calvinkatoroy/pandu-capstone/weekly/WEEK_3/LAPORAN PEKANAN INDIVIDU - Calvin Wirathama Katoroy - Pekan 3.docx

# LAPORAN PEKANAN INDIVIDU

## Capstone Project Desain Proyek 2

### A. Identitas Mahasiswa

Item | Keterangan
Nama | Calvin Wirathama Katoroy
NPM | 2306242395
Program Studi | Teknik Elektro
Kelompok | 13
Judul Proyek | P.A.N.D.U (Perangkat Alarm Nirkabel Deteksi Urgensi)
Pekan ke- | 3
Periode Tanggal | 7 - 12 September 2026
Dosen Pembimbing | Tomy Abuzairi, S.T., M.Sc., Ph.D.

## B. Target Mingguan

Target yang direncanakan pada awal pekan berdasarkan WBS dan pembagian tugas kelompok.

No | Target Pekerjaan | Luaran yang Diharapkan | Status
1 | Melakukan persiapan perancangan mockup dashboard awal sesuai layout device yang akan ditentukan | Wireframe/referensi desain dashboard monitoring | ☐ Belum ☑ Selesai
2 | Mendukung review skematik rangkaian Vest Node, Helmet Node, dan Edge Gateway bersama tim hardware | Masukan teknis kebutuhan data untuk dashboard | ☐ Belum ☑ Selesai
3 | Memantau kelanjutan finalisasi system design tim sebelum tahap procurement | Catatan hasil review desain sistem | ☐ Belum ☑ Selesai

## C. Logbook Aktivitas Harian

Hari/Tanggal | Uraian Aktivitas | Waktu (Jam) | Bukti/Dokumen
Senin (7 Sep) | Mengumpulkan referensi UI/UX dashboard monitoring perangkat wearable & tracking untuk acuan desain P.A.N.D.U | 3 | Kumpulan referensi desain
Selasa (8 Sep) | Menyusun wireframe awal layout dashboard (peta live tracking, status alarm, log insiden) | 4 | Sketsa wireframe dashboard
Rabu (9 Sep) | Diskusi dengan tim hardware terkait data yang dihasilkan skematik Vest Node & Helmet Node untuk kebutuhan tampilan dashboard | 3 | Notulensi diskusi
Kamis (10 Sep) | Merancang mockup dashboard awal menggunakan Figma sesuai draft layout device | 5 | Draft mockup dashboard (Figma)
Jumat (11 Sep) | Meninjau hasil skematik rangkaian (Vest Node, Helmet Node, Edge Gateway) di EasyEDA Pro bersama tim | 3 | Catatan review skematik
Sabtu (12 Sep) | Merapikan dan mendokumentasikan hasil mockup dashboard awal pekan ini | 4 | Dokumen mockup dashboard (update)

### Total Jam Kerja Minggu Ini: 22 Jam

## D. Realisasi Pekerjaan

### 1. Aktivitas yang Berhasil Diselesaikan

Tuliskan hasil pekerjaan yang benar-benar telah selesai.

- Menyelesaikan riset referensi dan wireframe awal untuk mockup dashboard monitoring P.A.N.D.U (live tracking lokasi, status alarm, dan log insiden) sesuai arahan layout device yang direncanakan.
- Membuat draft mockup dashboard awal menggunakan Figma sebagai acuan visual sebelum layout device final ditentukan.
- Ikut meninjau dan memberikan masukan pada skematik rangkaian Vest Node, Helmet Node, dan Edge Gateway yang difinalisasi tim hardware di EasyEDA Pro, khususnya terkait data yang perlu ditampilkan di dashboard.

### 2. Luaran yang Dihasilkan

Wireframe/referensi desain dashboard monitoring

- Draft mockup dashboard awal (Figma)
- Catatan masukan teknis hasil review skematik rangkaian

## E. Capaian Teknis Mingguan

### Komponen/Subsistem yang Dikerjakan (pilih sesuai tugas)

Subsistem | Target | Realisasi | Persentase
Hardware | - | - | -
Software | Perancangan mockup dashboard awal sesuai layout device | Wireframe & draft mockup dashboard (Figma) selesai disusun | 100%
Mekanik | - | - | -
Pengujian | - | - | -
Dokumentasi | Dokumentasi hasil diskusi & review skematik rangkaian | Notulensi diskusi dan catatan review terdokumentasi | 100%

### Ringkasan Kemajuan

Persiapan perancangan mockup dashboard awal (wireframe & draft Figma) telah diselesaikan 100% sebagai tugas individu pekan ini, sejalan dengan progres kelompok yang telah menyelesaikan perancangan skematik rangkaian dan finalisasi system design (progres total proyek ~24,25%). Mockup dashboard akan dilanjutkan dan disesuaikan pekan depan setelah layout device final ditentukan.

## F. Permasalahan dan Kendala

No | Kendala | Dampak | Tingkat Risiko
1 | Layout final device (dimensi & tampilan) belum ditentukan karena blueprint casing baru selesai pada pekan ini | Desain mockup dashboard masih bersifat sementara dan berpotensi perlu revisi | Rendah

### Analisis Penyebab

Kendala utama berasal dari ketergantungan desain dashboard terhadap blueprint 2D casing yang baru difinalisasi tim mekanik pada pekan ini, sehingga proporsi dan orientasi tampilan pada mockup dashboard belum dapat dipastikan sepenuhnya.

G. Tindakan Korektif dan Solusi

Kendala | Solusi/Tindak Lanjut | PIC | Target Penyelesaian
Layout final device belum ditentukan | Menggunakan dimensi blueprint 2D casing (55 x 65 x 18 mm) sebagai acuan sementara untuk proporsi mockup dashboard, sambil menunggu konfirmasi layout final | Calvin, Adhi Rajasa Rafif | 19 September 2026

H. Dokumentasi Kemajuan

Lampirkan:

- Foto kegiatan
- Foto perangkat/prototipe
- Screenshot software/dashboard
- Hasil pengujian
- Diagram revisi
- Bukti commit Git
- Bukti pembelian atau pengadaan (jika relevan)

Minimal 2-3 dokumentasi setiap pekan.

I. Kontribusi Terhadap Tim

### Koordinasi yang Dilakukan

- Rapat tim tanggal: 11 September 2026 (review skematik rangkaian & progres perancangan)
- Diskusi teknis: Kebutuhan data dashboard berdasarkan skematik Vest Node, Helmet Node, dan Edge Gateway; penyesuaian mockup dashboard dengan blueprint casing
- Koordinasi dengan dosen: Belum ada sesi khusus minggu ini; pembahasan dilakukan internal tim

### Kontribusi Pribadi

Berperan dalam menyusun wireframe dan draft mockup dashboard awal untuk sistem PANDU, serta memberikan masukan teknis pada review skematik rangkaian Vest Node, Helmet Node, dan Edge Gateway bersama tim hardware.

J. Evaluasi Diri

### Yang Berjalan Baik

- Persiapan mockup dashboard dapat diselesaikan tepat waktu meski layout device belum final.
- Koordinasi dengan tim hardware terkait kebutuhan data dashboard berjalan lancar.
- Review skematik rangkaian dilakukan secara kolaboratif dan menghasilkan masukan yang relevan.

### Yang Perlu Diperbaiki

- Perlu koordinasi lebih awal dengan tim mekanik agar dimensi/layout device tersedia sebelum mulai mendesain mockup dashboard.
- Dokumentasi progres mockup sebaiknya disimpan secara bertahap (versioning), bukan hanya di akhir pekan.
- Komunikasi dengan dosen pembimbing perlu ditingkatkan agar arah desain dashboard segera divalidasi.

### Pelajaran yang Didapat Minggu Ini

- Desain antarmuka (dashboard) sebaiknya menunggu kepastian parameter fisik perangkat (dimensi, layout) agar tidak banyak revisi.
- Kolaborasi lintas subsistem (hardware-software) penting agar dashboard benar-benar merepresentasikan data yang tersedia dari perangkat.
- Blueprint teknis yang presisi dari tim mekanik mempercepat proses desain antarmuka pada tahap berikutnya.

K. Rencana Pekan Berikutnya

No | Rencana Kegiatan | Target Luaran | Estimasi Jam
1 | Menyelesaikan perancangan mockup dashboard sesuai layout device final (bersama Rafif) | Mockup dashboard (high-fidelity) siap direview tim | 8 Jam
2 | Mendukung proses check out/pemesanan komponen yang telah direncanakan | Bukti pemesanan komponen | 3 Jam
3 | Mengikuti perkembangan PCB design & 3D model untuk menyesuaikan referensi visual dashboard bila diperlukan | Catatan penyesuaian (jika ada) | 3 Jam

## L. Persetujuan

Mahasiswa


Nama: Calvin Wirathama Katoroy

Tanda tangan:

____________

Tanggal: 12 September 2026


Ketua Kelompok

Nama: Adhi Rajasa Rafif

Tanda tangan:

____________

Tanggal: 12 September 2026

Catatan Pembimbing
