calvinkatoroy/pandu-capstone/weekly/WEEK_2/Template LAPORAN KEMAJUAN Pekanan.pdf

# LAPORAN KEMAJUAN PEKANAN

DESAIN PROYEK TEKNIK ELEKTRO, KOMPUTER,

# BIOMEDIK 2

Judul Proyek | : Perangkat Alarm Nirkabel Deteksi Urgensi
Kelompok | : 13
Pekan Ke- | :
Periode | :
Dosen Pembimbing | : Tomy Abuzairi, S.T., M.Sc., Ph.D.
Ketua Kelompok | : Adhi Rajasa Rafif (2306266943)
Anggota Kelompok | :
- Calvin Wirathama Katoroy (2306242395)
- M Gibran Arya Avincena (2306156643)
- Muhammad Rifat Faqih (2306250762)
- Tri Yoga Arsyad (2306161920)

# 1. Ringkasan Kemajuan Pekanan

Tuliskan ringkasan kegiatan yang telah dilakukan selama satu Pekan terakhir.

Contoh:

Pada pekan ke-4 tim telah menyelesaikan implementasi modul sensor, melakukan pengujian komunikasi antara mikrokontroler dan server, serta memperbaiki bug pada antarmuka monitoring.

# 2. Target Pekan Ini

No | Target | Status
1 | Verifikasi Spesifikasi Seluruh Komponen | ☐ Tercapai ☐ Belum
2 | Pembuatan finalisasi Bills of Materials | ☐ Tercapai ☐ Belum
3 | On-site visit environment user | ☐ Tercapai ☐ Belum

# 3. Realisasi Kegiatan

No | Kegiatan | Penanggung Jawab | Hasil

1

2

3

# 4. Kemajuan Tiap Anggota

Nama | Tugas Pekan Ini | Persentase Penyelesaian

# 5. Hasil Implementasi

## Hardware

- Komponen yang telah direalisasikan:
- Status integrasi:

## Software

- Fitur yang telah selesai:
- Fitur yang masih dikembangkan:

## Mekanik/Biomedik (jika ada)

# 6. Dokumentasi Hasil

## Foto Kegiatan

(Lampirkan foto implementasi, perakitan, pengujian, atau diskusi tim)

Gambar 1 |
Gambar 2 |

## Screenshot Sistem

(Jika proyek berbasis software atau IoT)

# 7. Pengujian yang Dilakukan

Parameter | Target | Hasil | Status
| | | ☐ Lulus ☐ Tidak
| | | ☐ Lulus ☐ Tidak
| | | ☐ Lulus ☐ Tidak

## Analisis Singkat

Tuliskan interpretasi hasil pengujian.

Contoh:

Hasil pengujian menunjukkan tingkat akurasi sensor sebesar 96,2%, telah memenuhi target minimal 95%.

# 8. Kendala dan Solusi

Kendala | Dampak | Solusi yang Dilakukan

# 9. Deviasi Terhadap Jadwal

Aktivitas | Jadwal Awal | Realisasi | Keterangan
Pengujian Lapangan (Field Validation) | Minggu 14 | Minggu 15-16 (Skenario PoC)
4 | 4 | 4 | 4

## Analisis Deviasi

Jelaskan penyebab keterlambatan atau percepatan pekerjaan.

# 10. Rencana Kerja Pekan Berikutnya

No | Aktivitas | PIC | Target Selesai
1
2
3

# 11. Persentase Progress Proyek

Komponen | Bobot (%) | Progress (%)
Perancangan | 25 | 80
Implementasi Hardware | 20 | 0
Implementasi Software | 20 | 0
Integrasi Sistem | 15 | 0
Pengujian | 15 | 0
Dokumentasi | 5 | 25

## Progress Total Proyek

Progress Total = 16,25%

# 12. Kesimpulan

Studi lapangan telah dilakukan untuk memvalidasi kebutuhan PANDU. Hasilnya menjadi dasar penyempurnaan rancangan sistem dan persiapan proof of concept sebelum memasuki tahap implementasi.

# Persetujuan

Jabatan | Nama | Tanda Tangan
Ketua Kelompok
Pembimbing
